AlirezaAsna/head-md-ai-families/images/final/IMG_3869.JPG

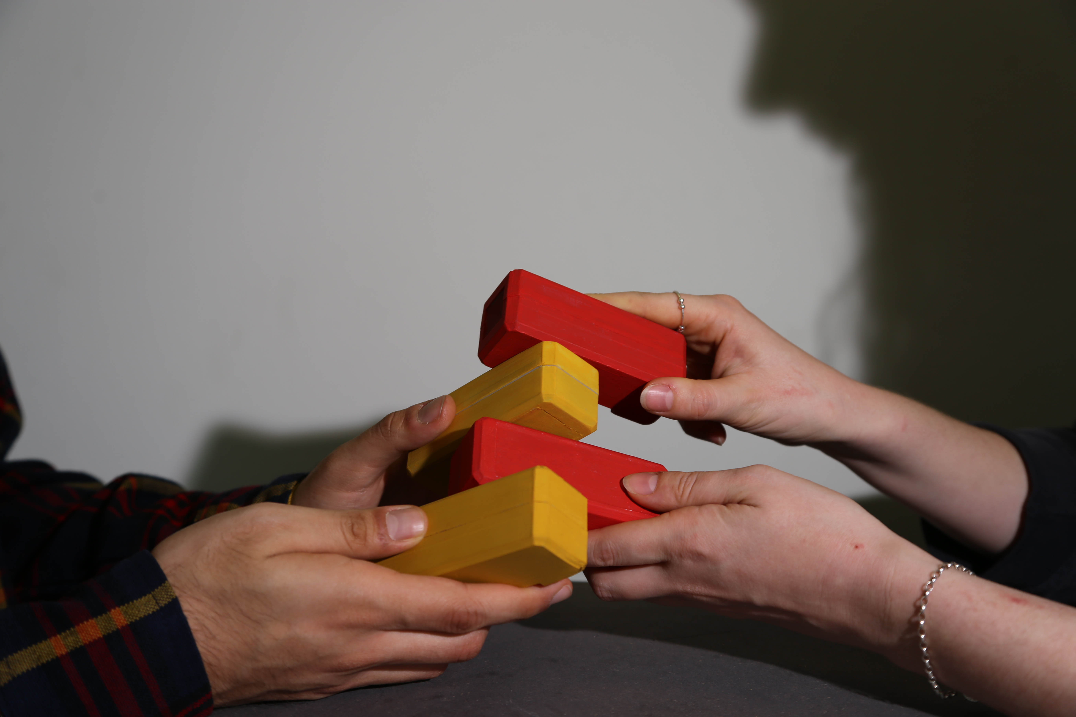
images/final/IMG_3869.JPG
