AlirezaAsna/head-md-ai-families/images/final/IMG_3872.JPG

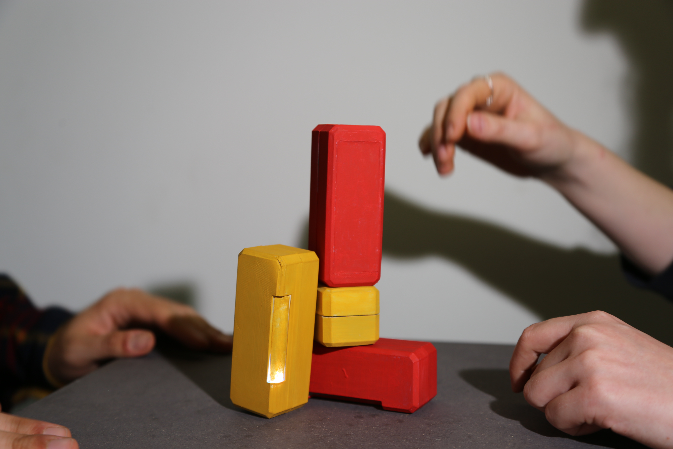
images/final/IMG_3872.JPG
