AlirezaAsna/head-md-ai-families/images/final/IMG_3876.JPG

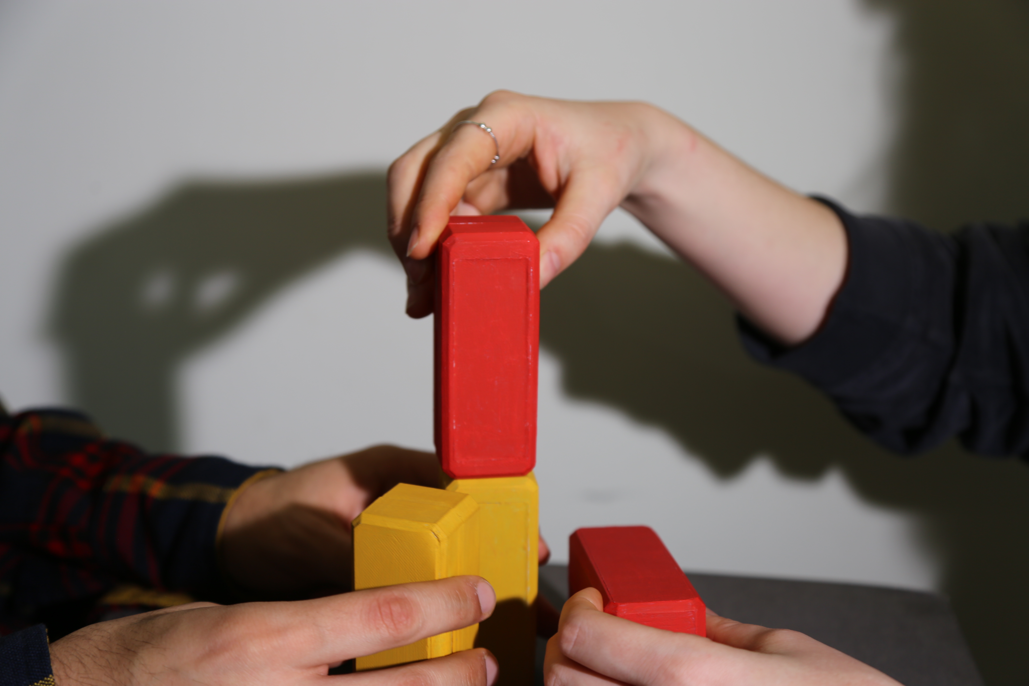
images/final/IMG_3876.JPG
