AlirezaAsna/head-md-ai-families/images/final/IMG_3880.JPG

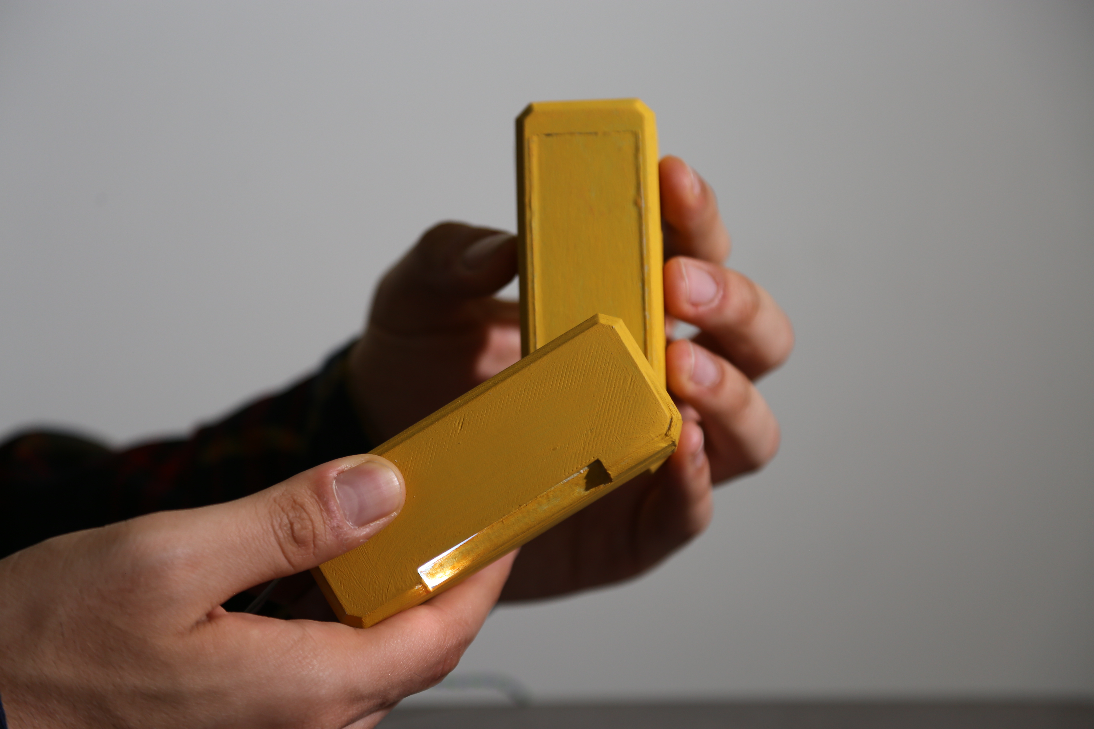
images/final/IMG_3880.JPG
