AlirezaAsna/head-md-ai-families/images/final/IMG_3882.JPG

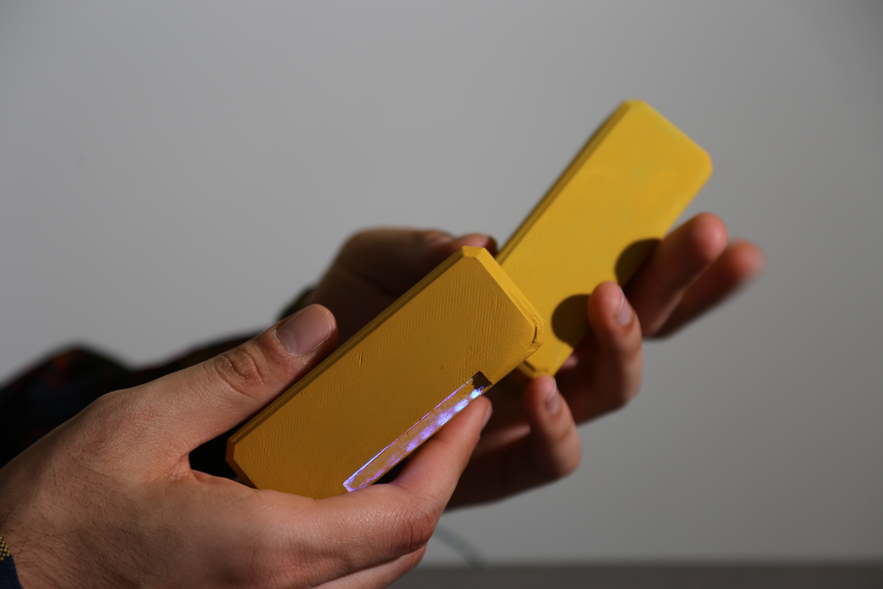
images/final/IMG_3882.JPG
