AlirezaAsna/head-md-ai-families/images/final/IMG_3889.JPG

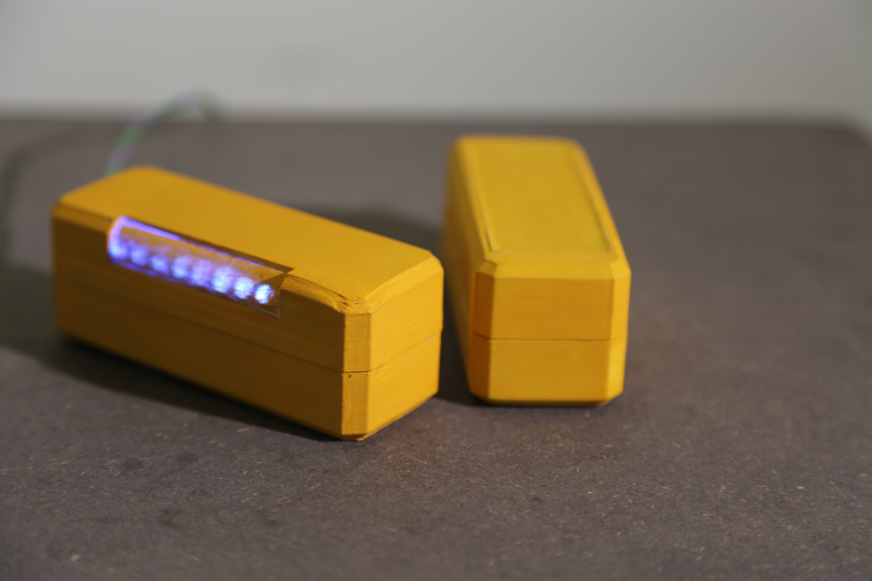
images/final/IMG_3889.JPG
