AlirezaAsna/head-md-ai-families/images/final/IMG_3912.JPG

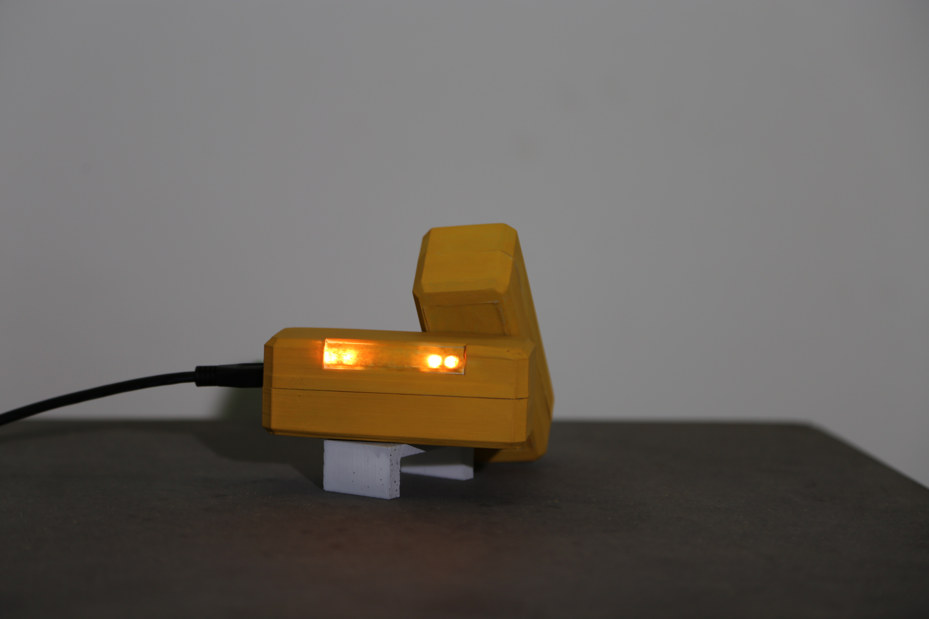
images/final/IMG_3912.JPG
