AlirezaAsna/head-md-ai-families/images/ideation/IMG_3755.JPG

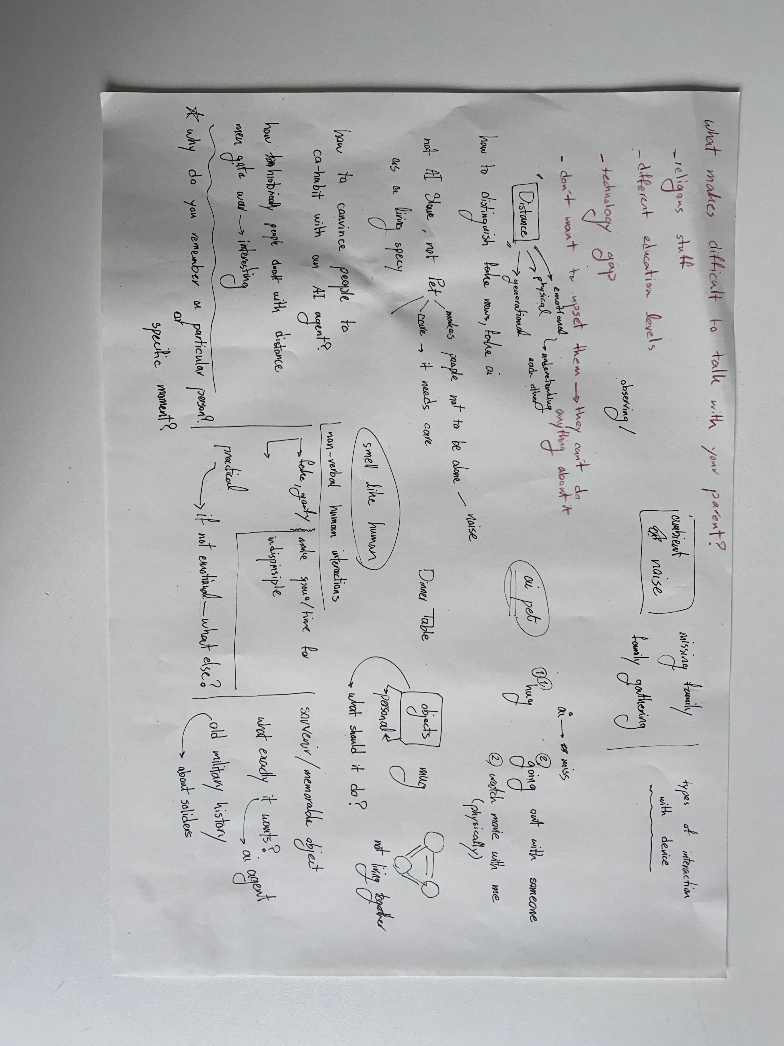
images/ideation/IMG_3755.JPG
