AlirezaAsna/head-md-ai-families/images/ideation/IMG_3756.JPG

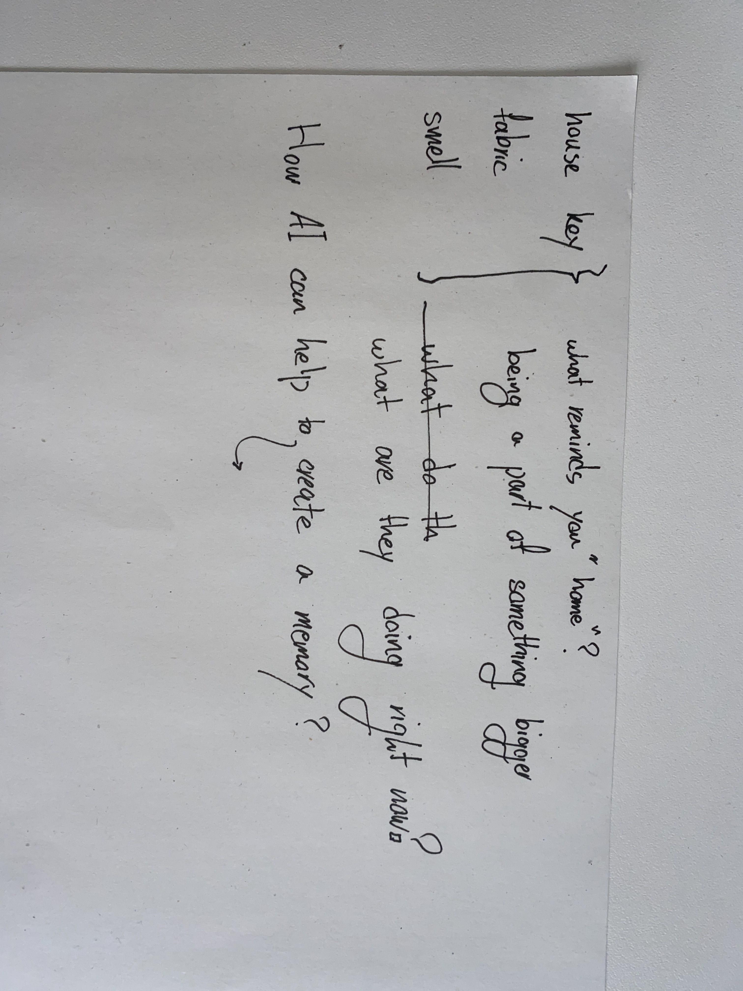
images/ideation/IMG_3756.JPG
