AlirezaAsna/head-md-ai-families/images/ideation/IMG_3757.JPG

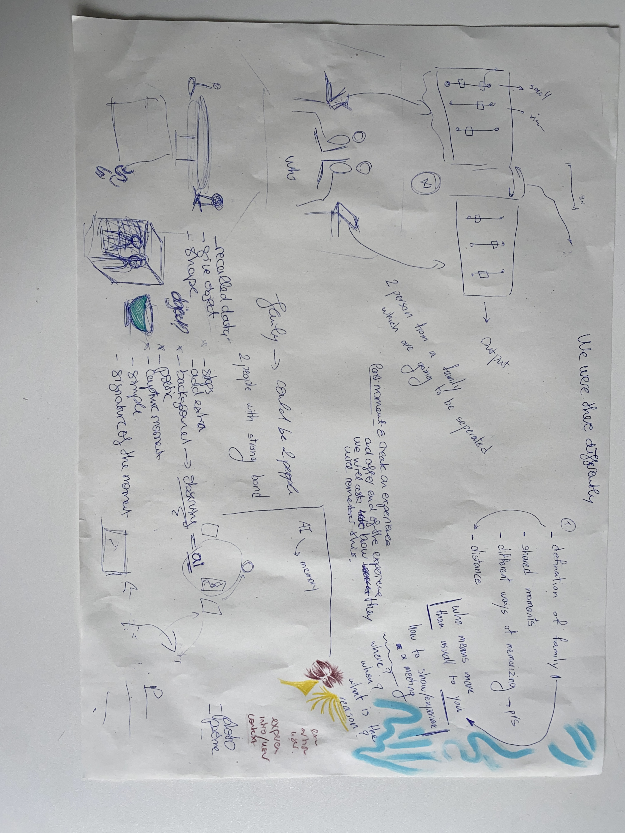
images/ideation/IMG_3757.JPG
