AlirezaAsna/head-md-ai-families/images/ideation/IMG_3758.JPG

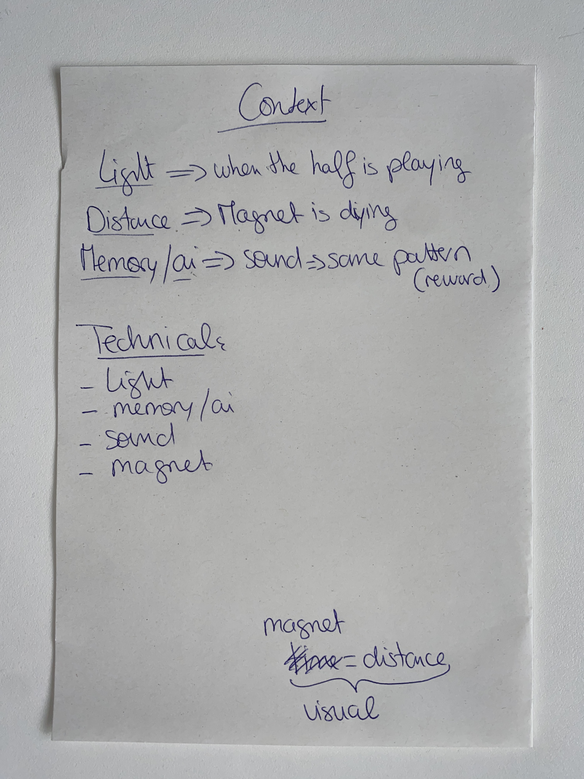
images/ideation/IMG_3758.JPG
