AlirezaAsna/head-md-ai-families/images/ideation/IMG_3759.JPG

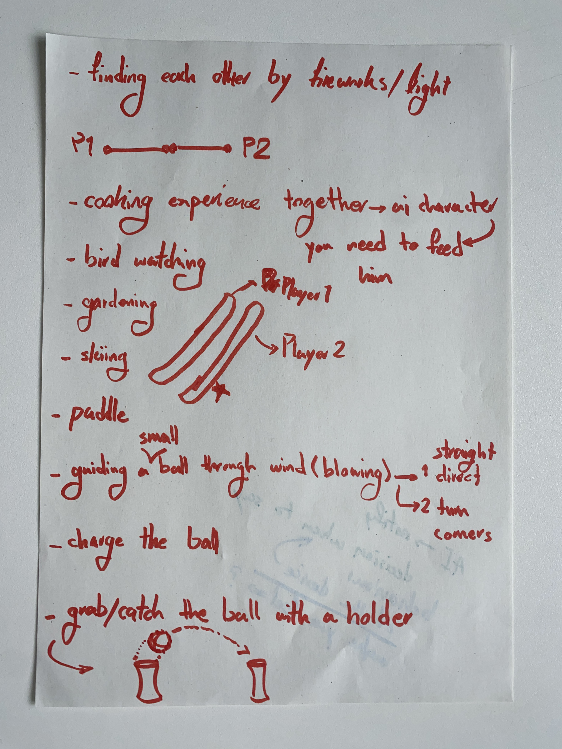
images/ideation/IMG_3759.JPG
