AlirezaAsna/head-md-ai-families/images/ideation/IMG_3760.JPG

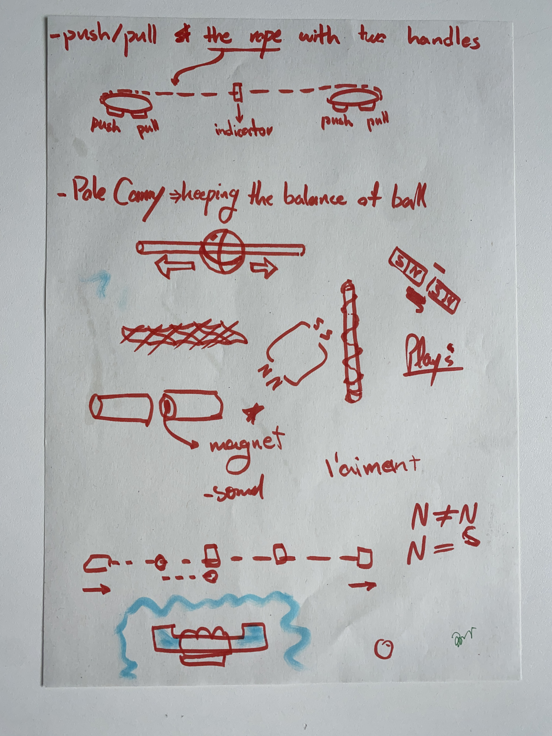
images/ideation/IMG_3760.JPG
