AlirezaAsna/head-md-ai-families/images/ideation/IMG_3761.JPG

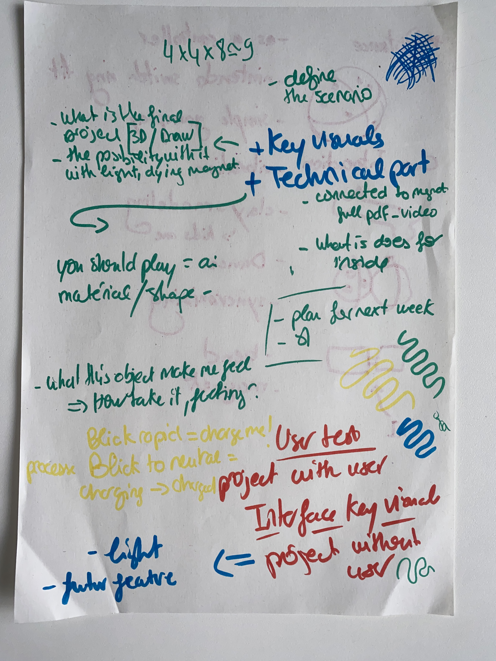
images/ideation/IMG_3761.JPG
