AlirezaAsna/head-md-ai-families/images/ideation/IMG_3762.JPG

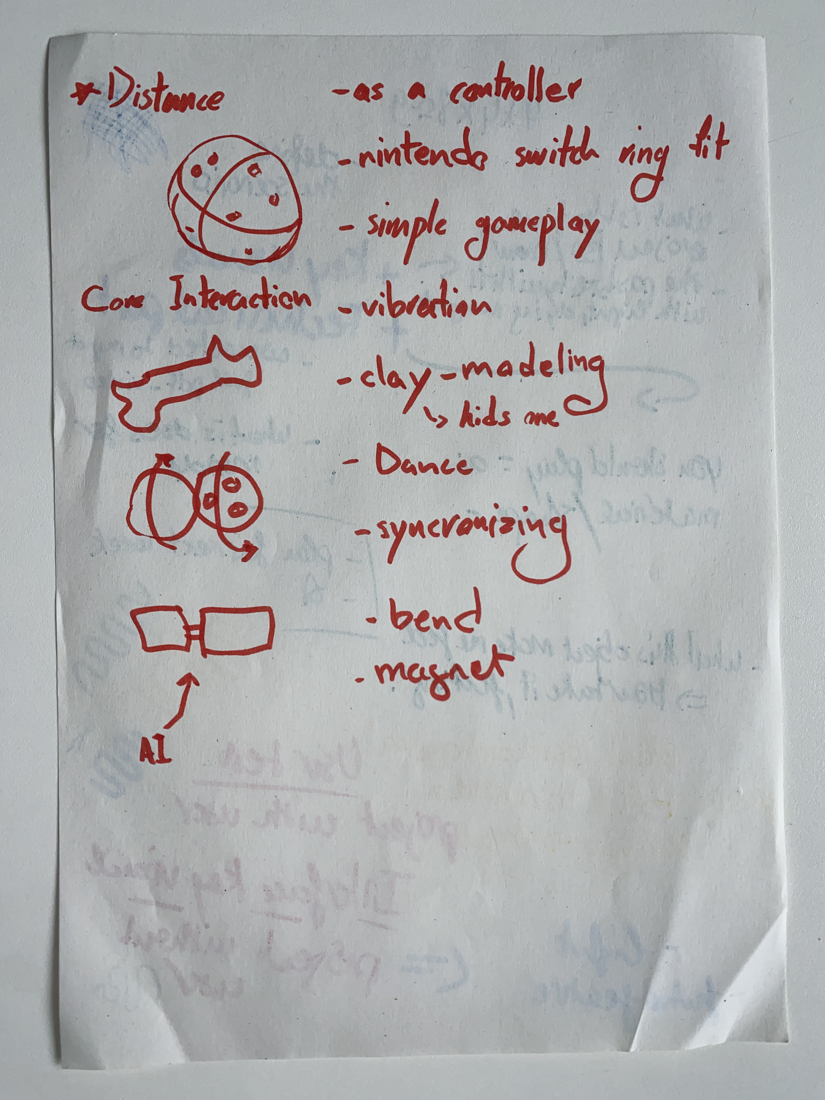
images/ideation/IMG_3762.JPG
