AlirezaAsna/head-md-ai-families/images/ideation/IMG_3763.JPG

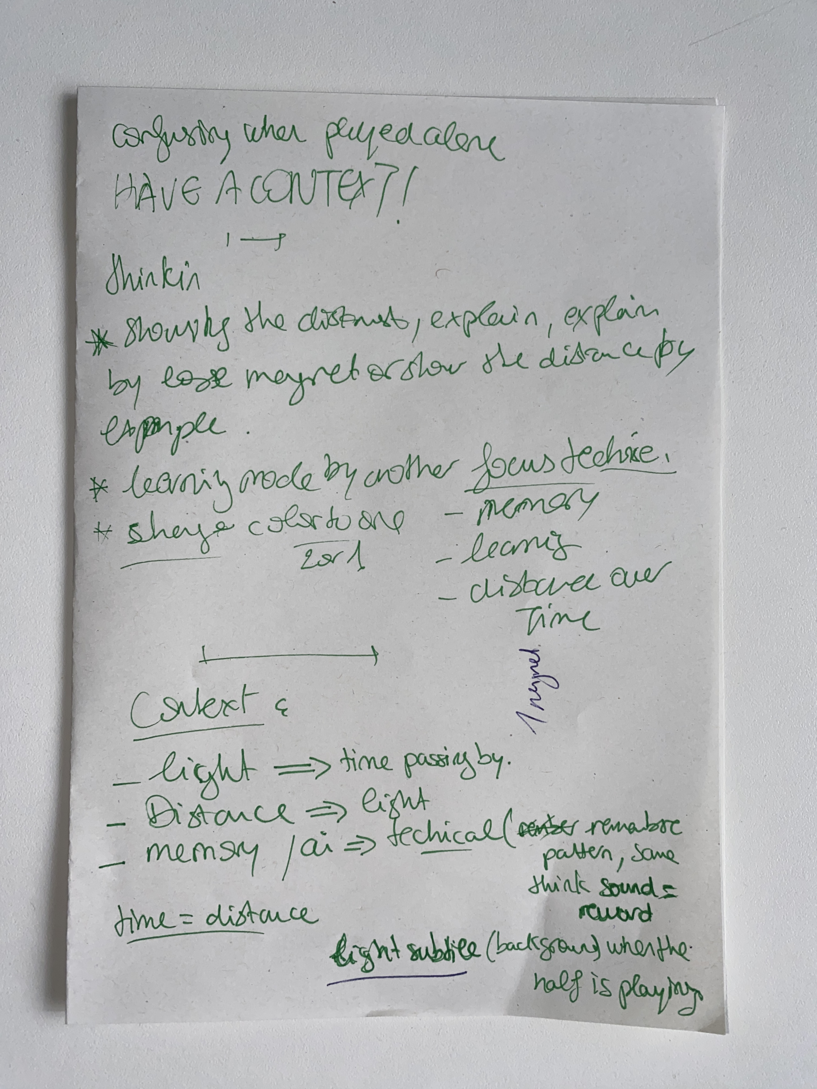
images/ideation/IMG_3763.JPG
