AlirezaAsna/head-md-ai-families/images/ideation/IMG_3764.JPG

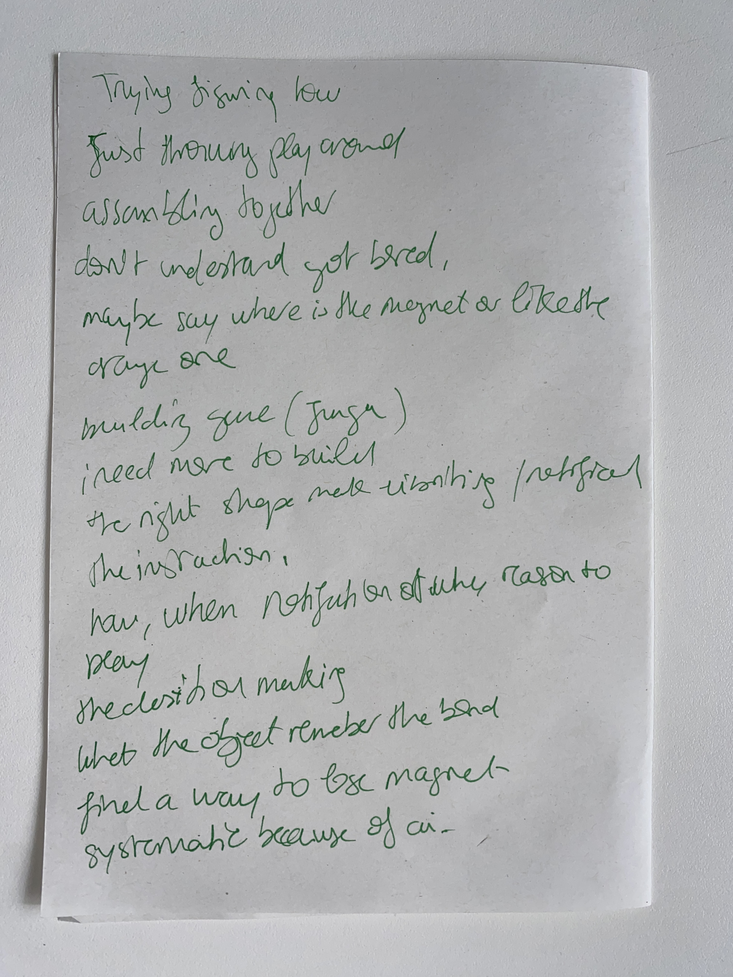
images/ideation/IMG_3764.JPG
