AlirezaAsna/head-md-ai-families/images/ideation/IMG_3765.JPG

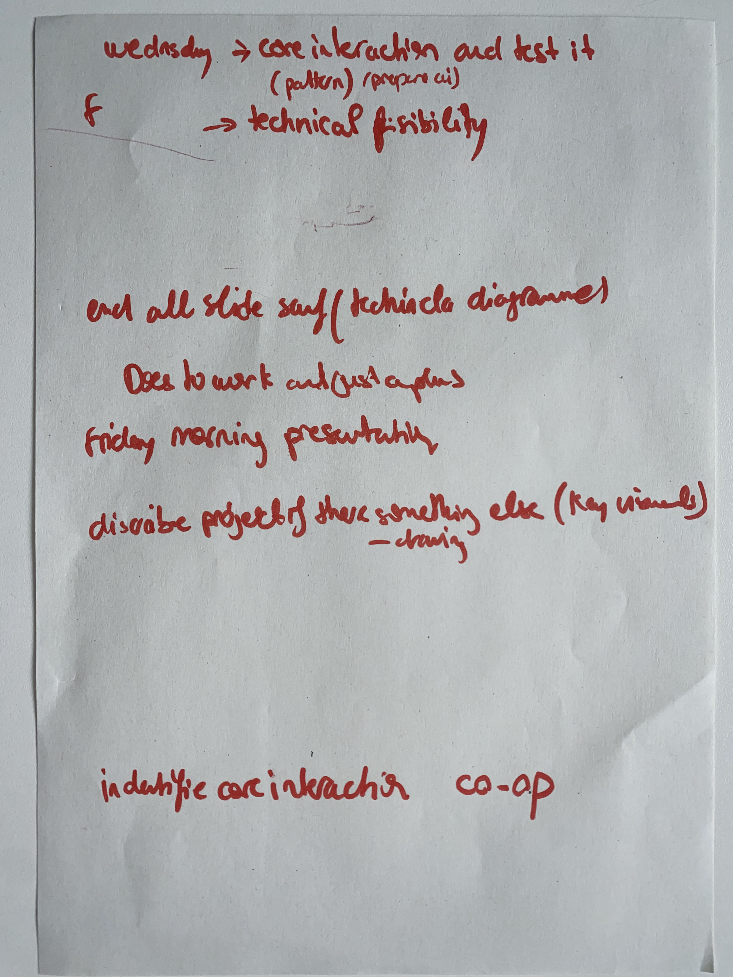
images/ideation/IMG_3765.JPG
