AlirezaAsna/head-md-ai-families/images/ideation/IMG_3766.JPG

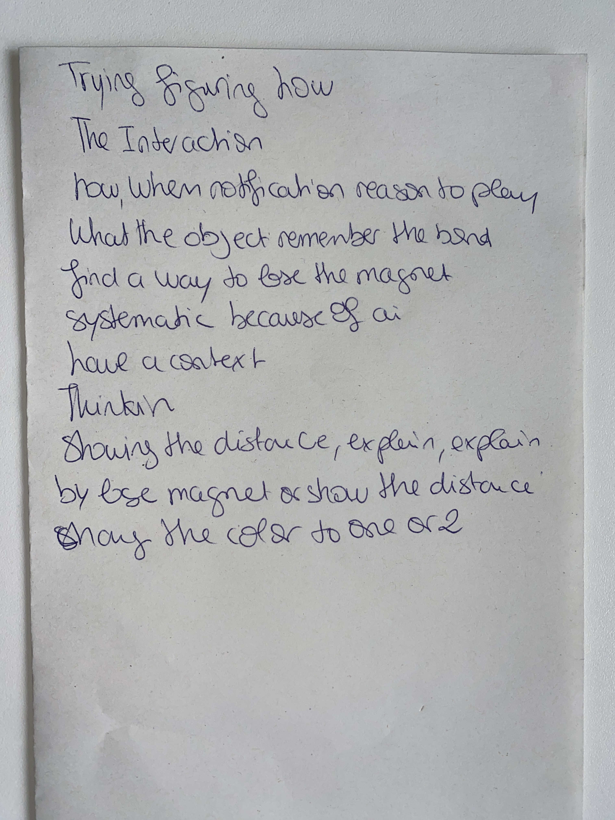
images/ideation/IMG_3766.JPG
