AlirezaAsna/head-md-ai-families/images/ideation/IMG_3767.JPG

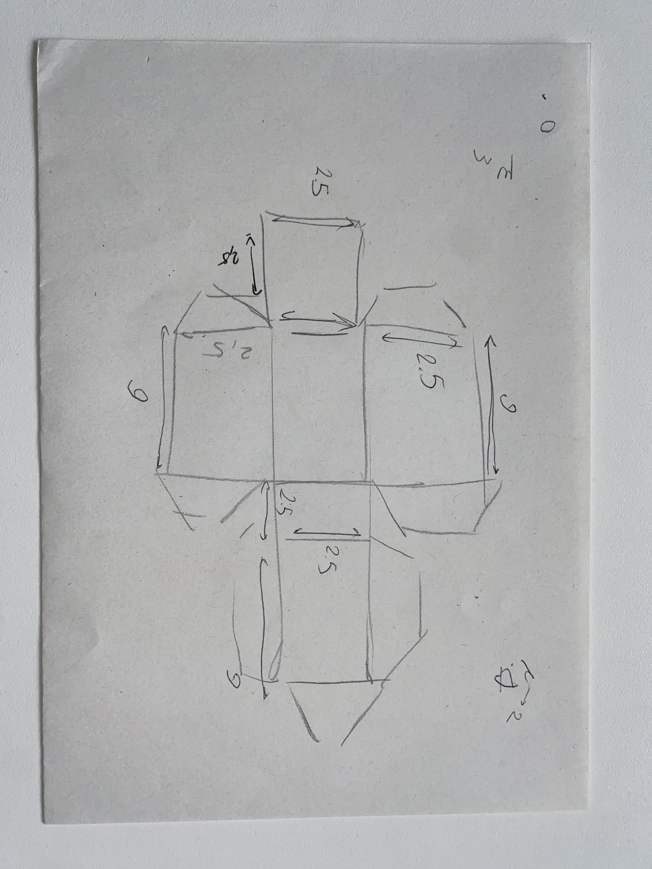
images/ideation/IMG_3767.JPG
