AlirezaAsna/head-md-ai-families/images/ideation/IMG_3768.JPG

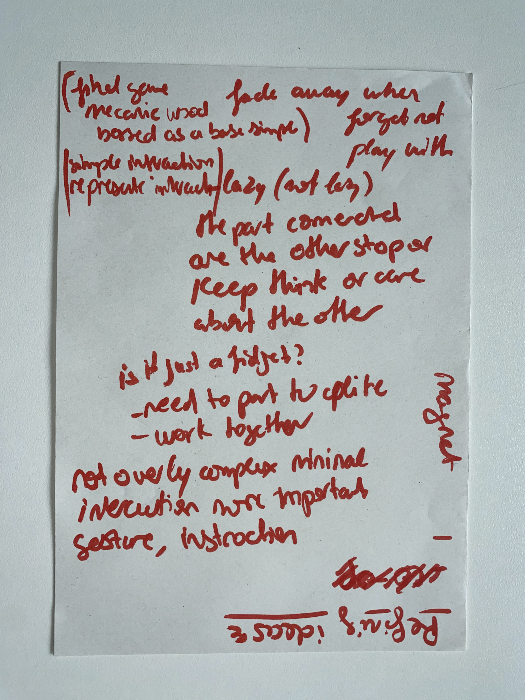
images/ideation/IMG_3768.JPG
