AlirezaAsna/head-md-ai-families/images/ideation/IMG_3770.JPG

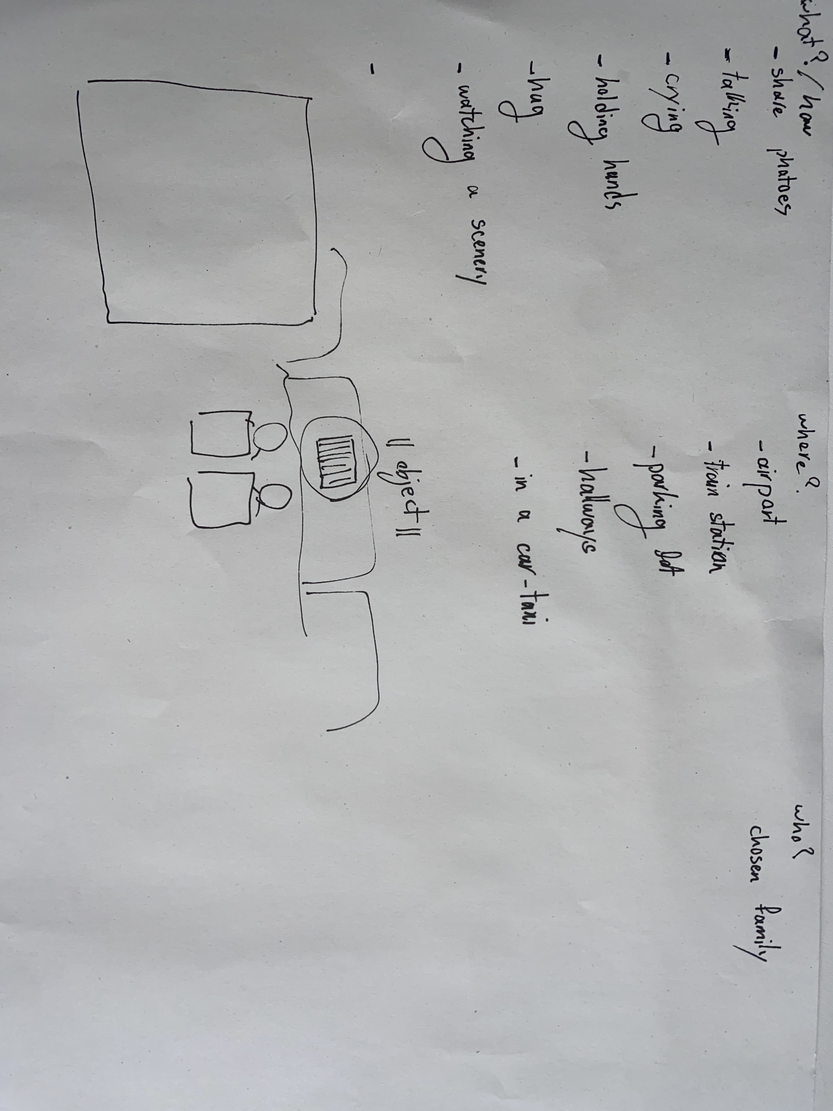
images/ideation/IMG_3770.JPG
