AlirezaAsna/head-md-ai-families/images/ideation/IMG_3771.JPG

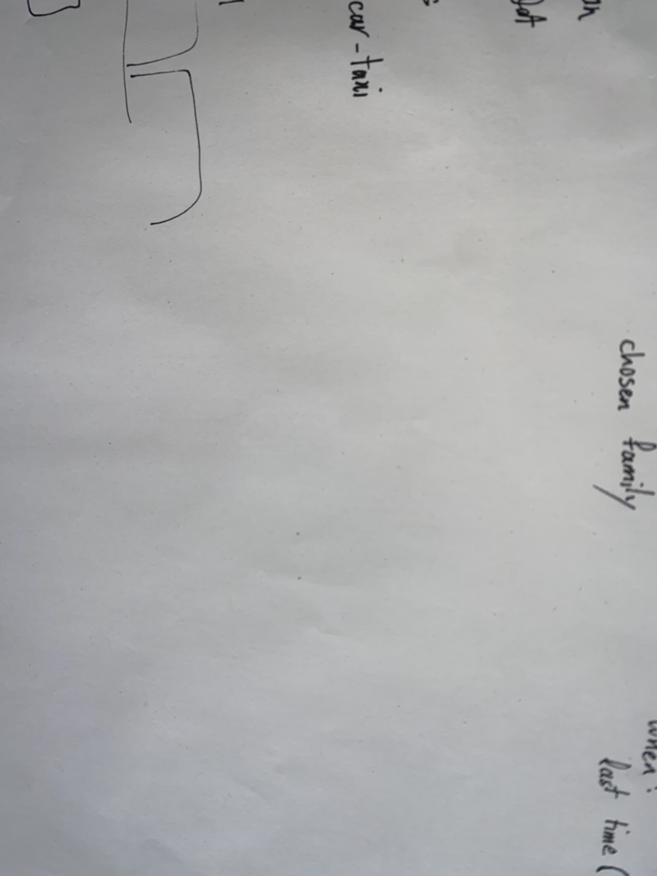
images/ideation/IMG_3771.JPG
