AlirezaAsna/head-md-ai-families/images/ideation/IMG_3772.JPG

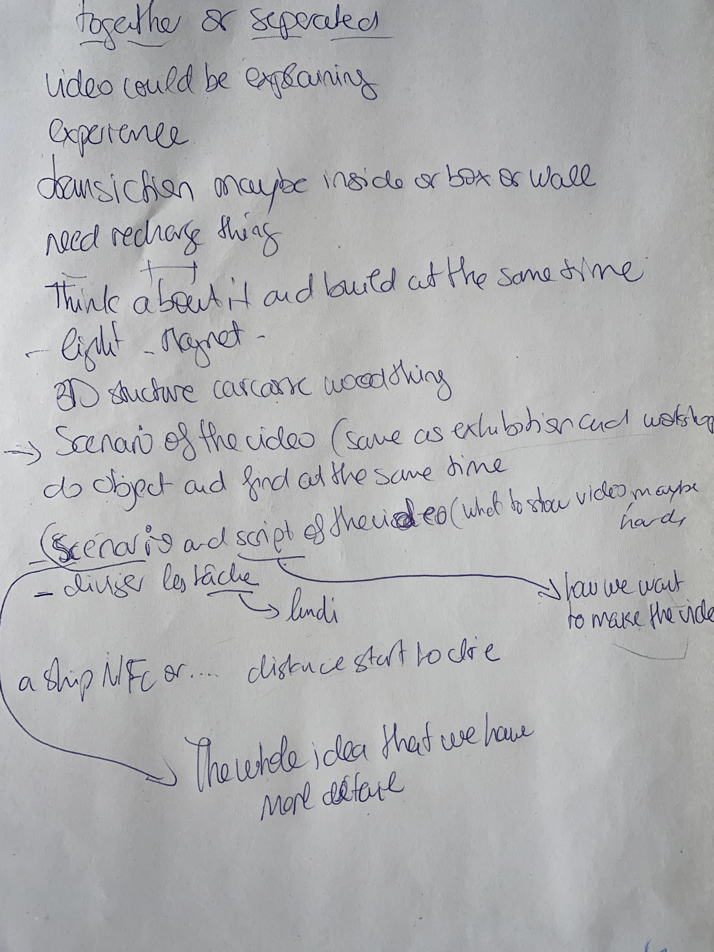
images/ideation/IMG_3772.JPG
