AlirezaAsna/head-md-ai-families/images/ideation/IMG_3773.JPG

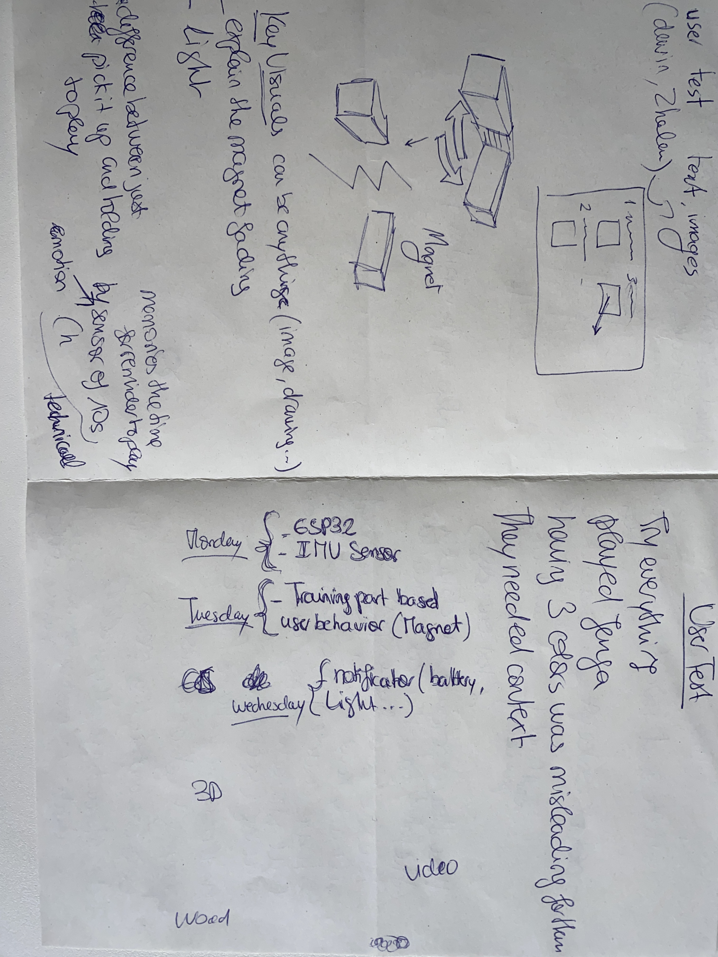
images/ideation/IMG_3773.JPG
