AlirezaAsna/head-md-ai-families/images/ideation/IMG_3774.JPG

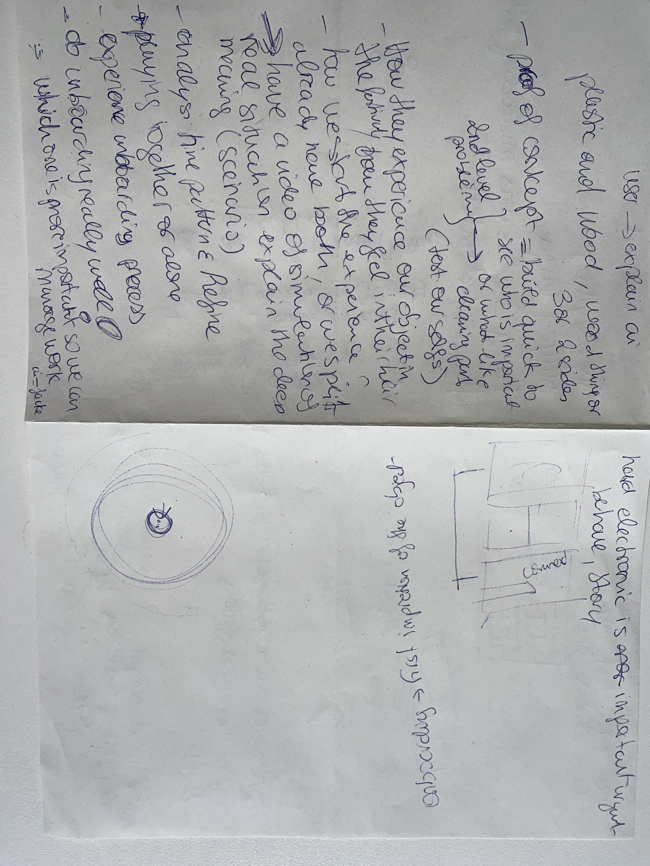
images/ideation/IMG_3774.JPG
