AlirezaAsna/head-md-ai-families/images/ideation/photo_2026-03-13_14-27-43.jpg

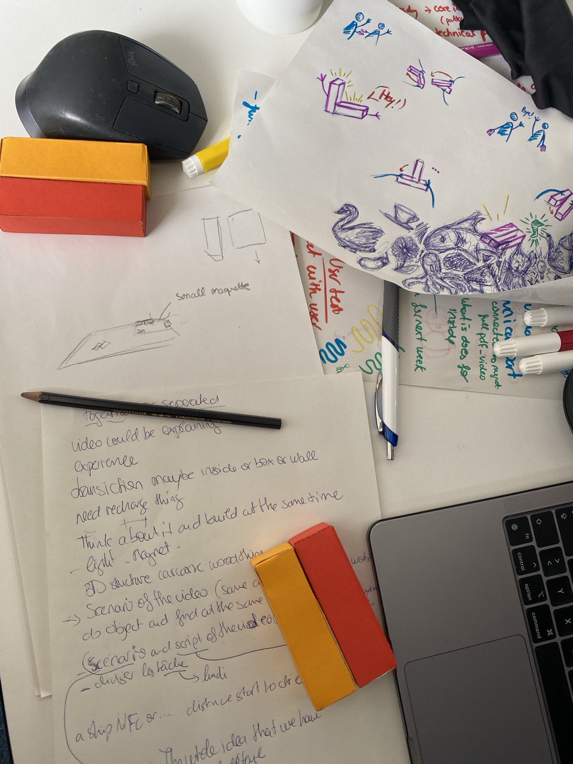
images/ideation/photo_2026-03-13_14-27-43.jpg
