AlirezaAsna/head-md-ai-families/images/process/IMG_3687.JPG

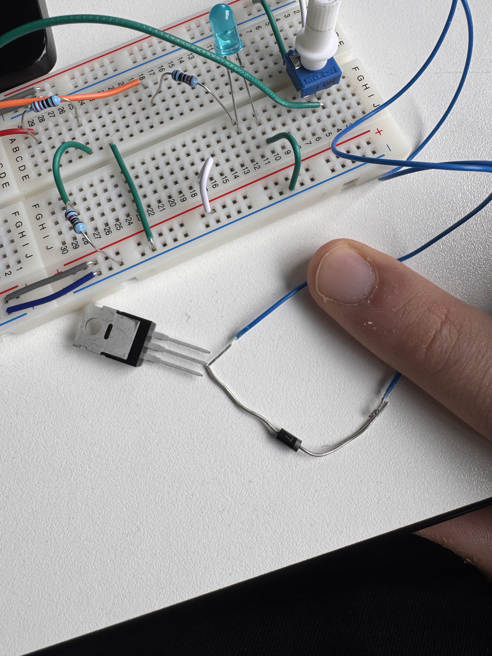
images/process/IMG_3687.JPG
