AlirezaAsna/head-md-ai-families/images/process/IMG_3693.JPG

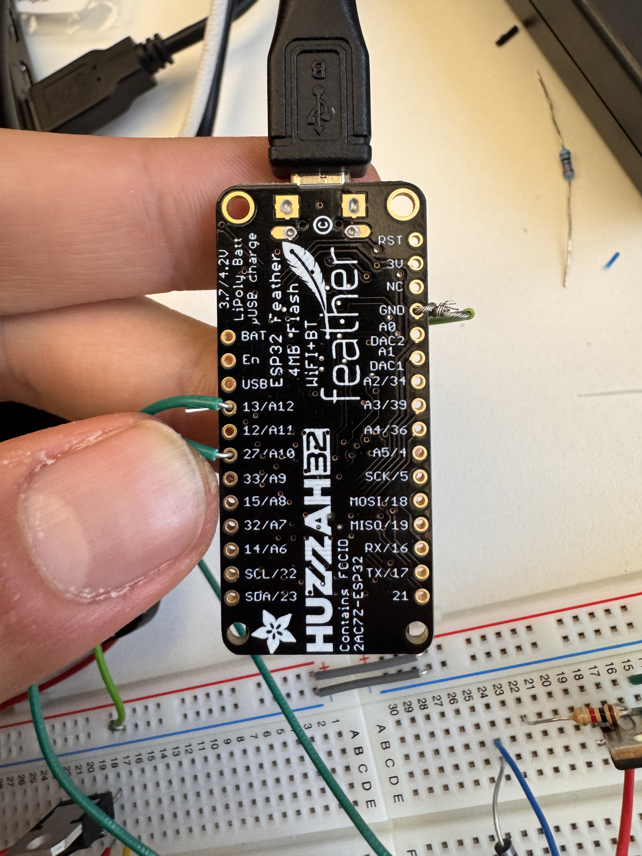
images/process/IMG_3693.JPG
