AlirezaAsna/head-md-ai-families/images/process/IMG_3699.JPG

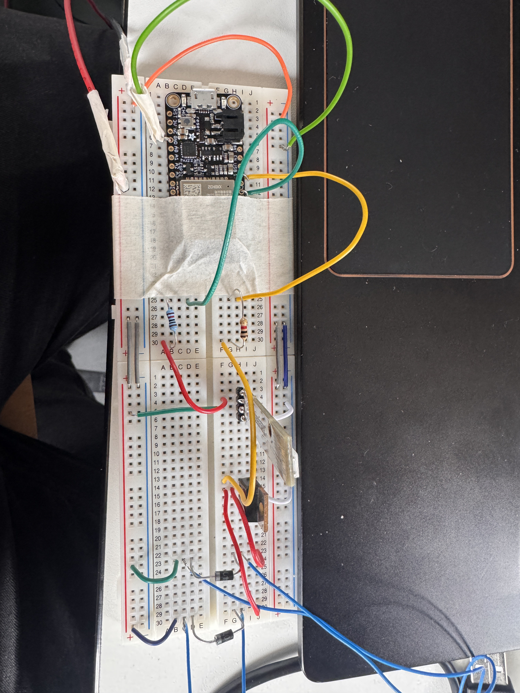
images/process/IMG_3699.JPG
