AlirezaAsna/head-md-ai-families/images/process/IMG_3701.JPEG

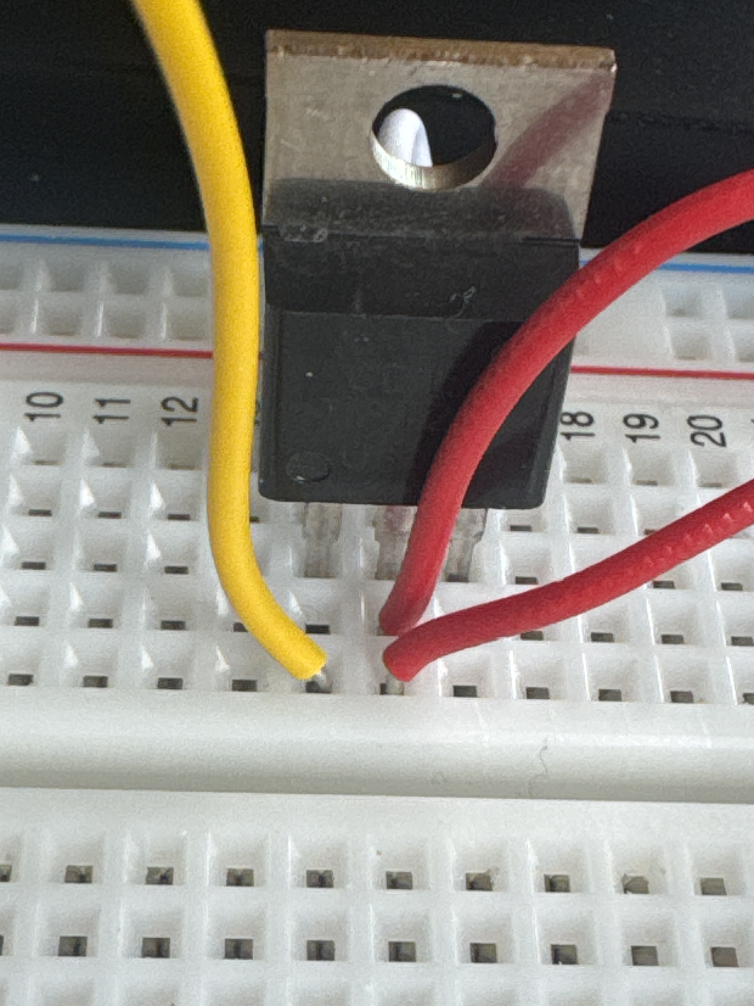
images/process/IMG_3701.JPEG
