AlirezaAsna/head-md-ai-families/images/process/IMG_3702.JPG

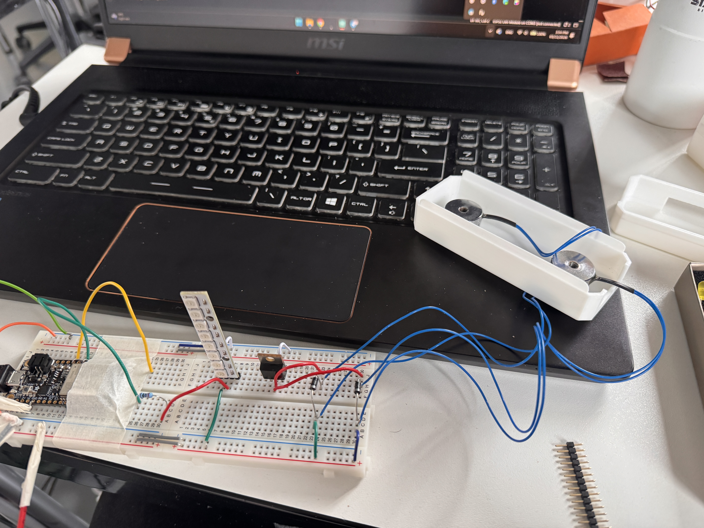
images/process/IMG_3702.JPG
