AlirezaAsna/head-md-ai-families/images/process/IMG_3703.JPG

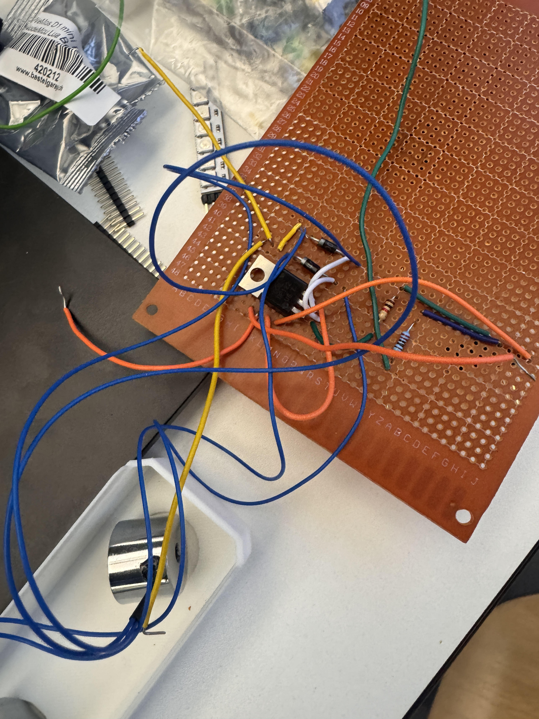
images/process/IMG_3703.JPG
