AlirezaAsna/head-md-ai-families/images/process/IMG_3715.JPG

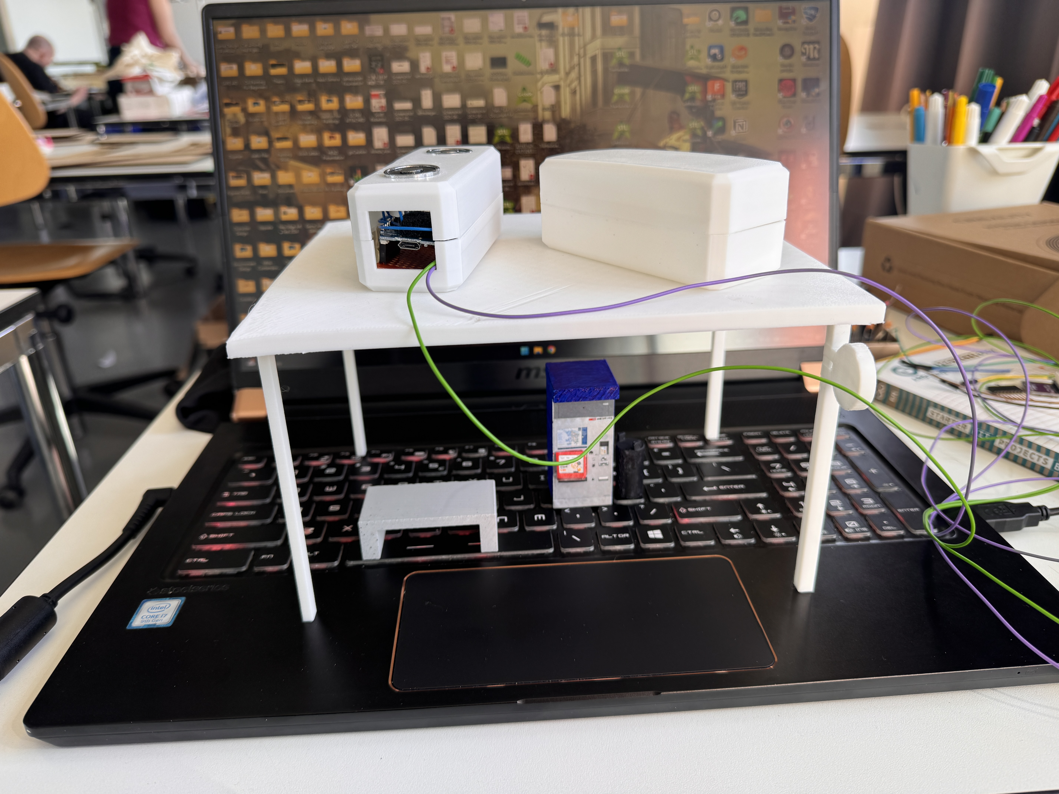
images/process/IMG_3715.JPG
