AlirezaAsna/head-md-ai-families/images/process/IMG_3724.JPG

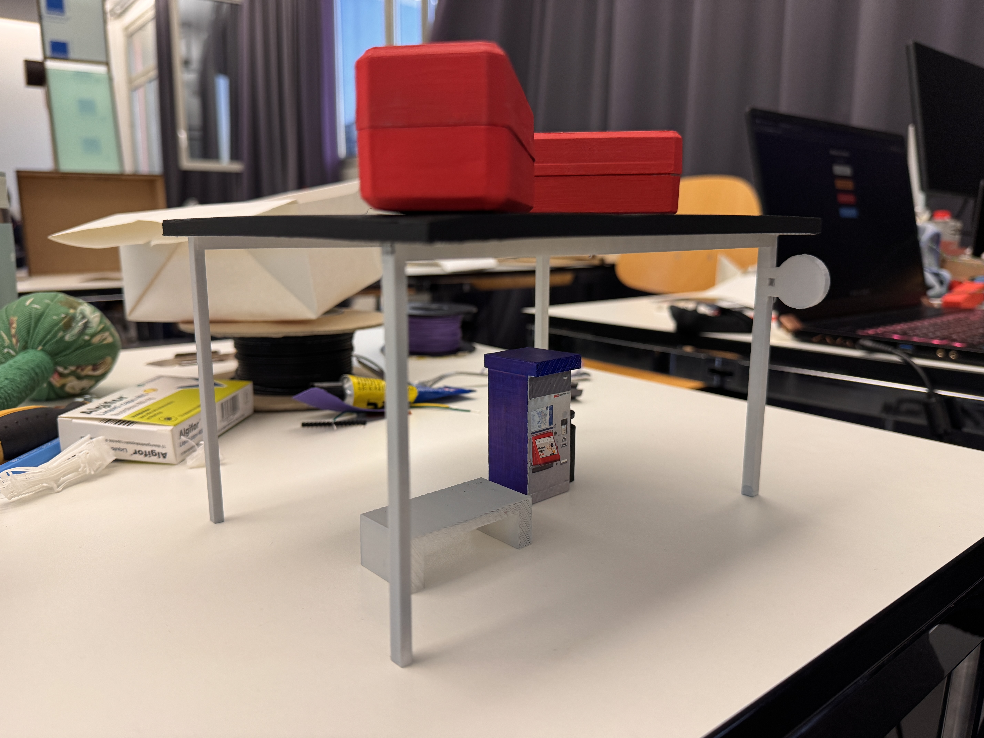
images/process/IMG_3724.JPG
