AlirezaAsna/head-md-ai-families/images/process/IMG_3725.JPG

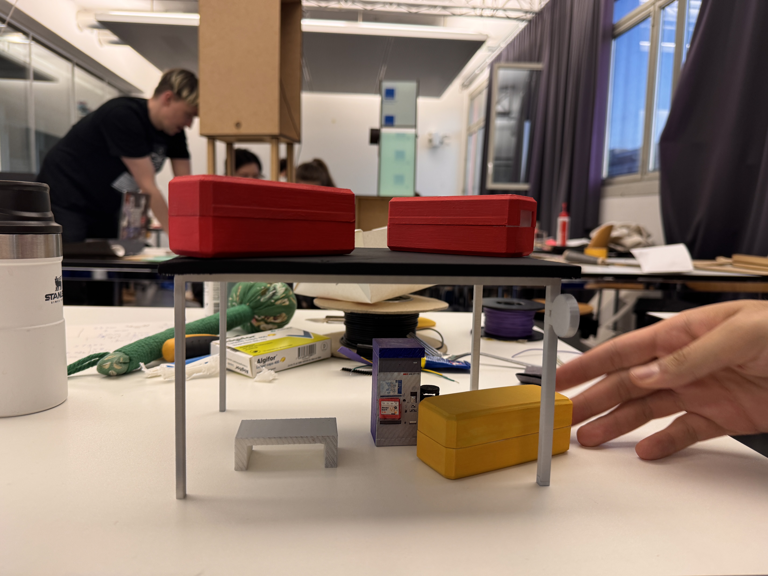
images/process/IMG_3725.JPG
