AlirezaAsna/head-md-ai-families/images/process/IMG_3727.JPG

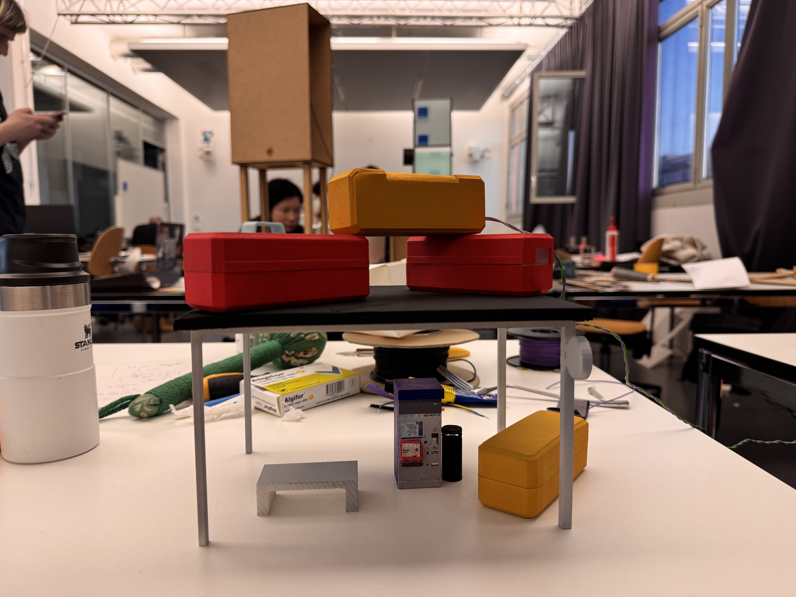
images/process/IMG_3727.JPG
