AlirezaAsna/head-md-ai-families/images/process/IMG_3728.JPG

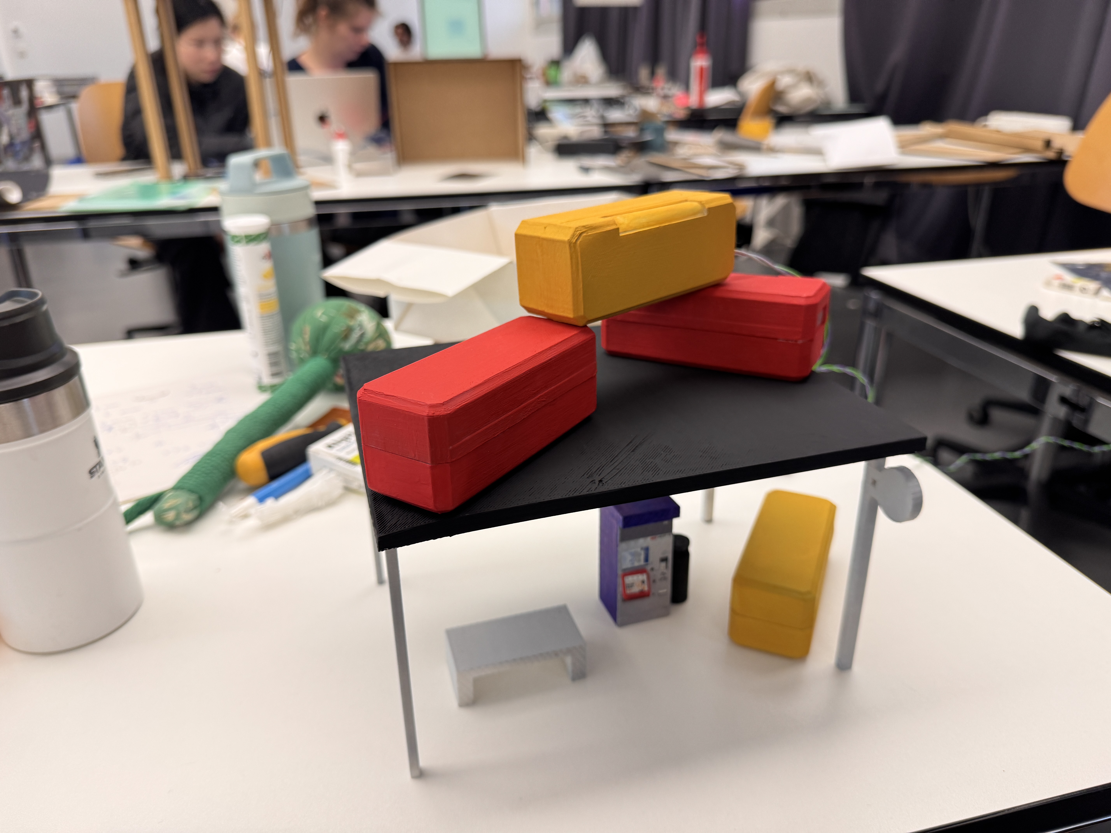
images/process/IMG_3728.JPG
