AlirezaAsna/head-md-ai-families/images/process/photo_2026-03-13_14-27-32.jpg

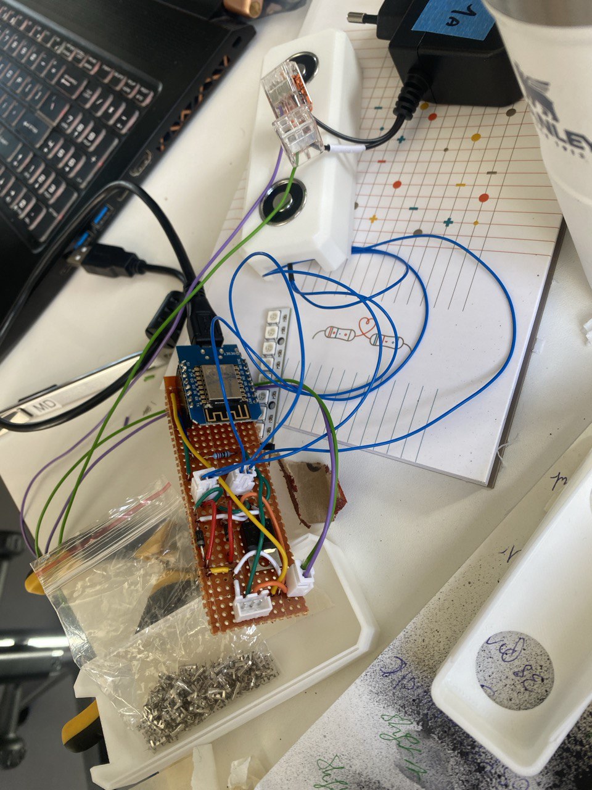
images/process/photo_2026-03-13_14-27-32.jpg
