AlirezaAsna/head-md-ai-families/images/renders/lightsOff.png

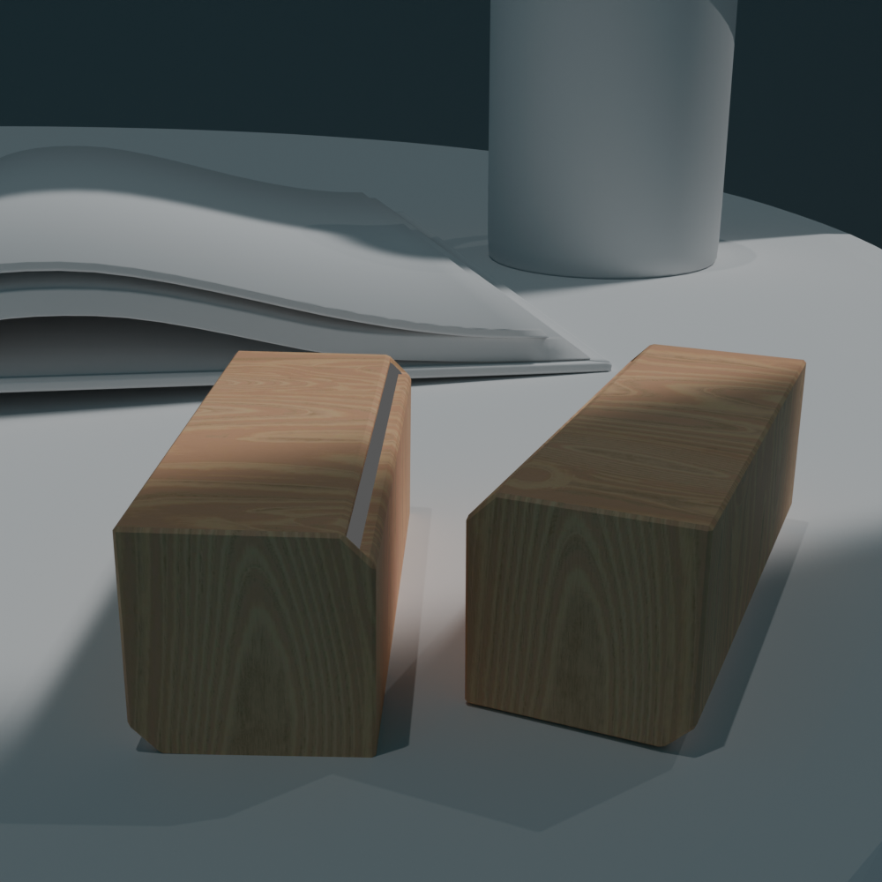
images/renders/lightsOff.png
