AlirezaAsna/head-md-ai-families/images/technical-diagram/technical diagram.png

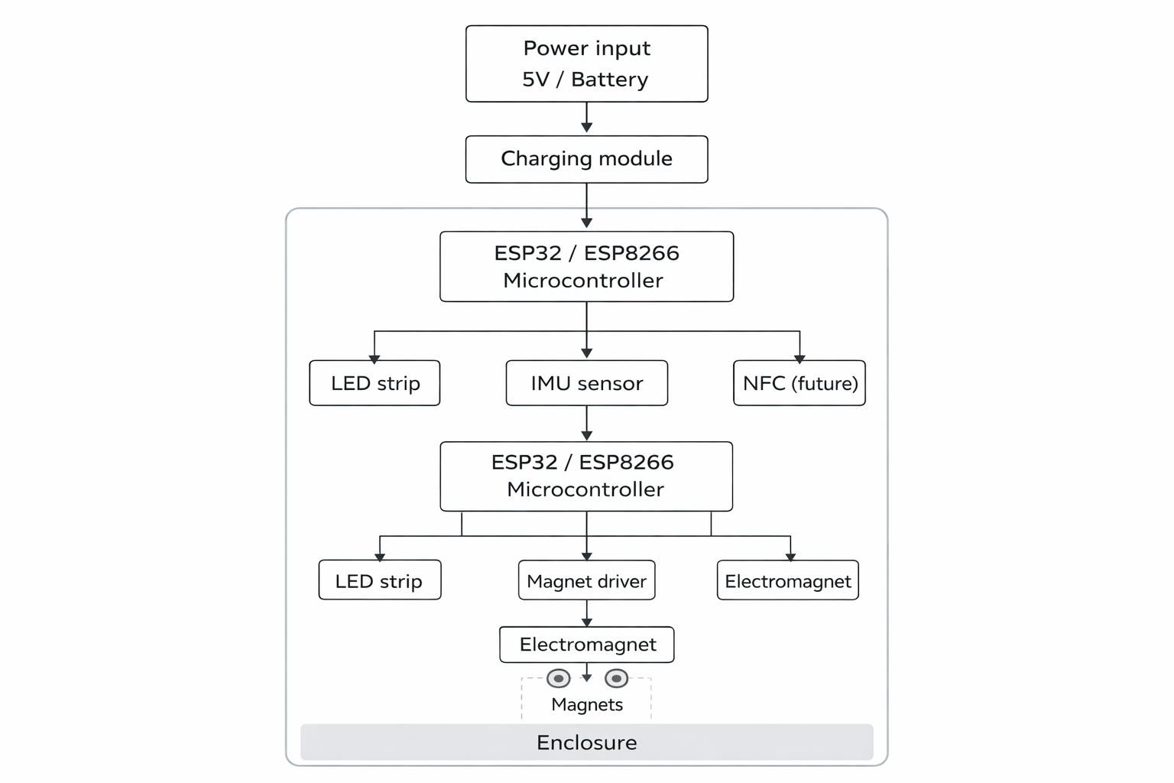
images/technical-diagram/technical diagram.png
