AlirezaAsna/head-md-ai-families/images/ideation/IMG_3754.JPG

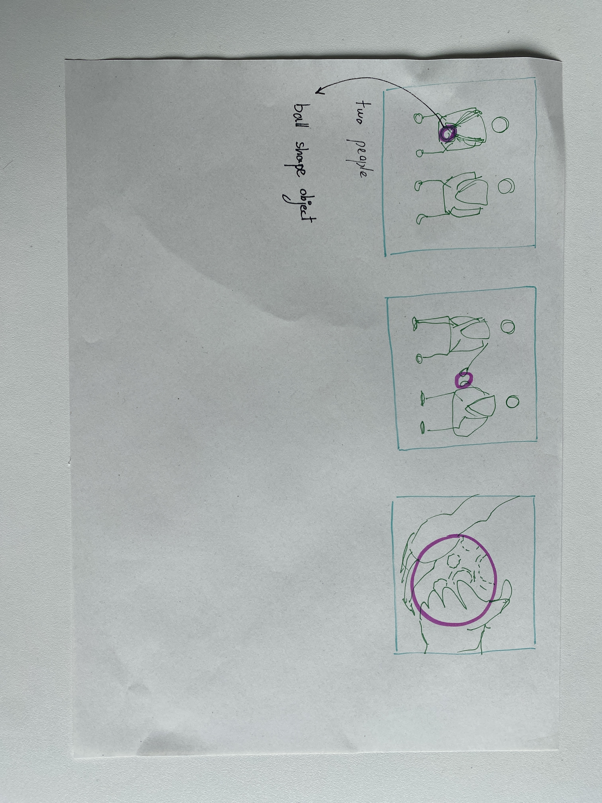
images/ideation/IMG_3754.JPG
