AlirezaAsna/head-md-ai-families/images/ideation/IMG_3769.JPG

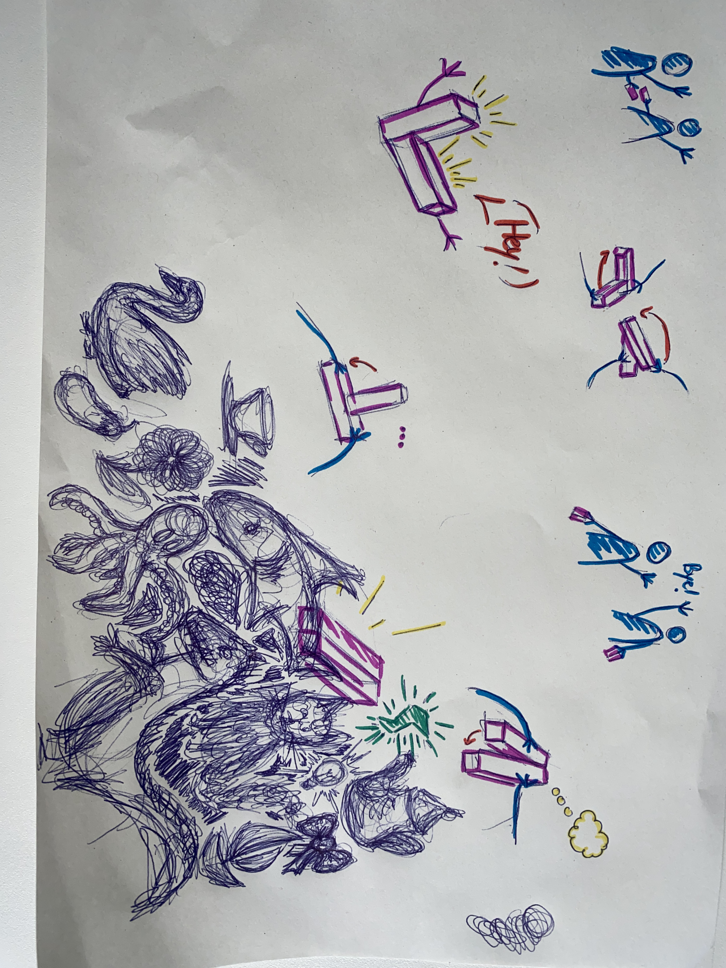
images/ideation/IMG_3769.JPG
