AlirezaAsna/head-md-ai-families/images/process/IMG_3681.JPG

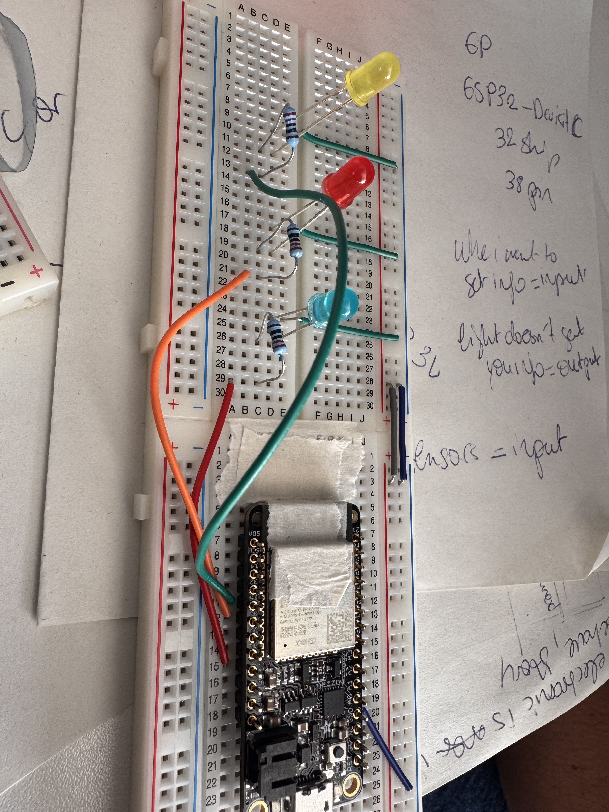
images/process/IMG_3681.JPG
