AlirezaAsna/head-md-ai-families/images/process/IMG_3685.JPG

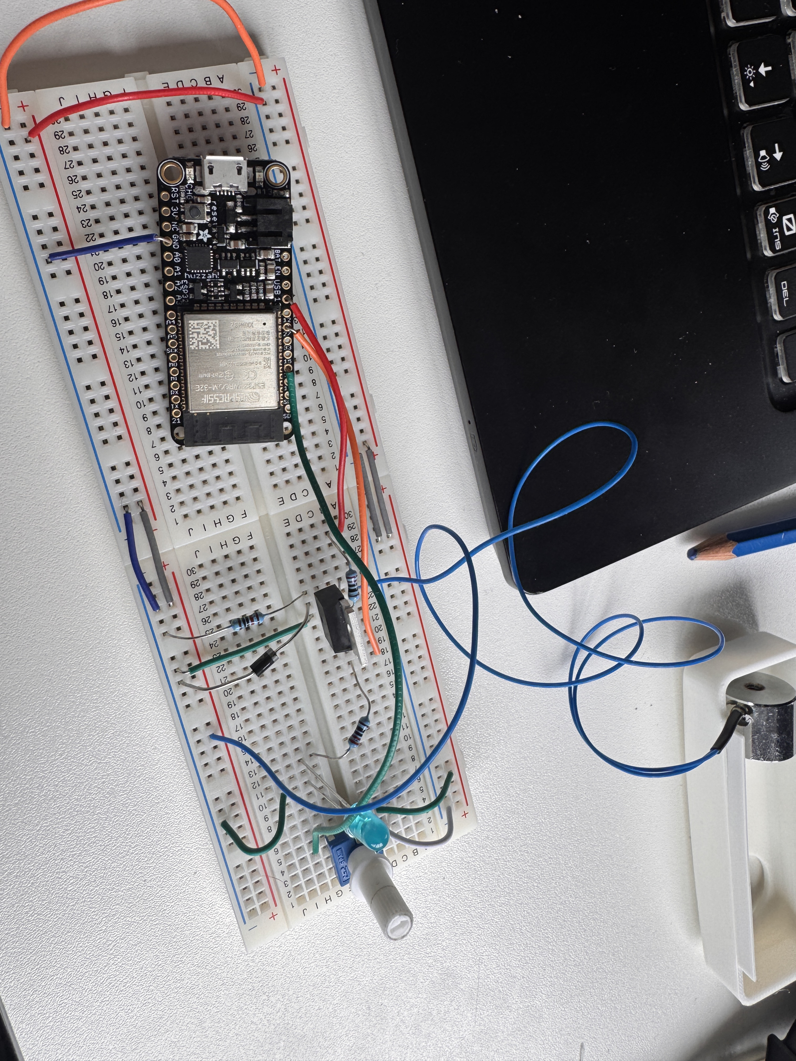
images/process/IMG_3685.JPG
