AlirezaAsna/head-md-ai-families/images/process/IMG_3688.JPG

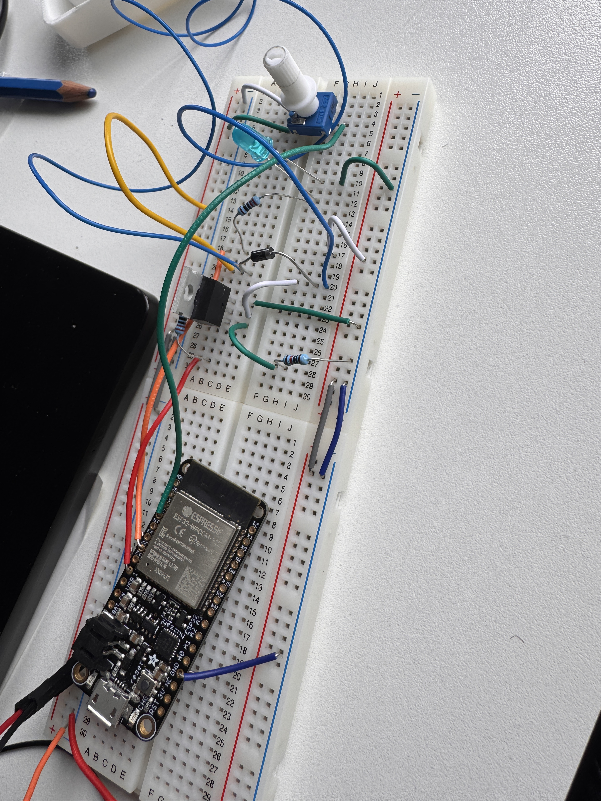
images/process/IMG_3688.JPG
