AlirezaAsna/head-md-ai-families/images/process/IMG_3689.JPG

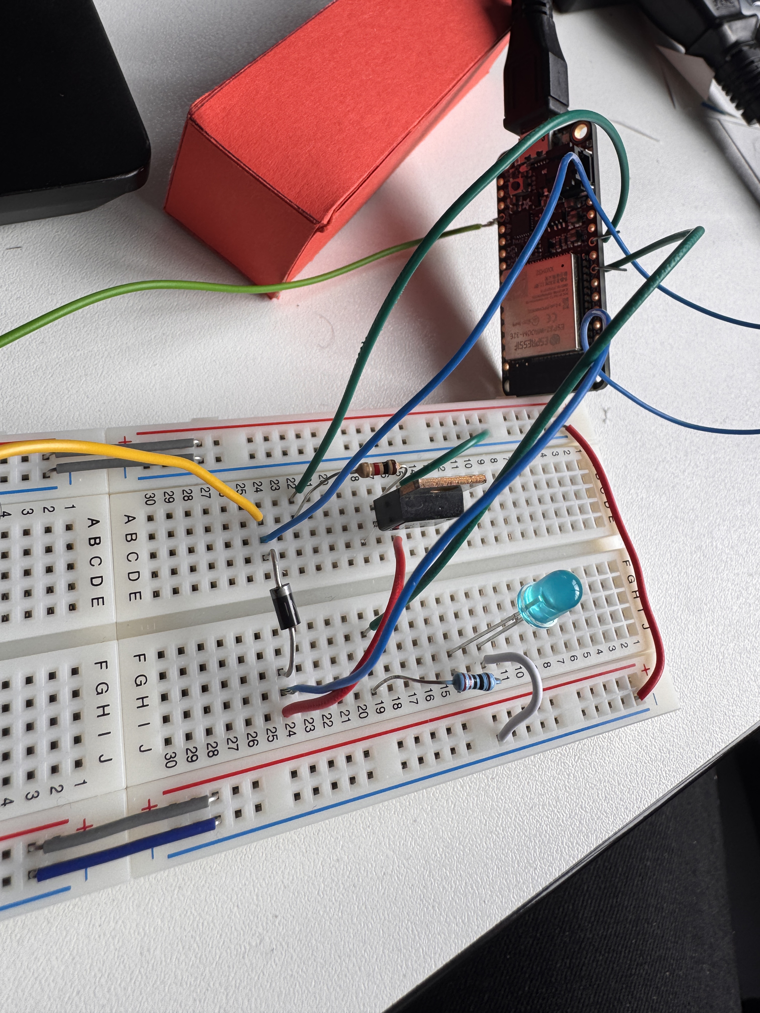
images/process/IMG_3689.JPG
