AlirezaAsna/head-md-ai-families/images/process/IMG_3690.JPG

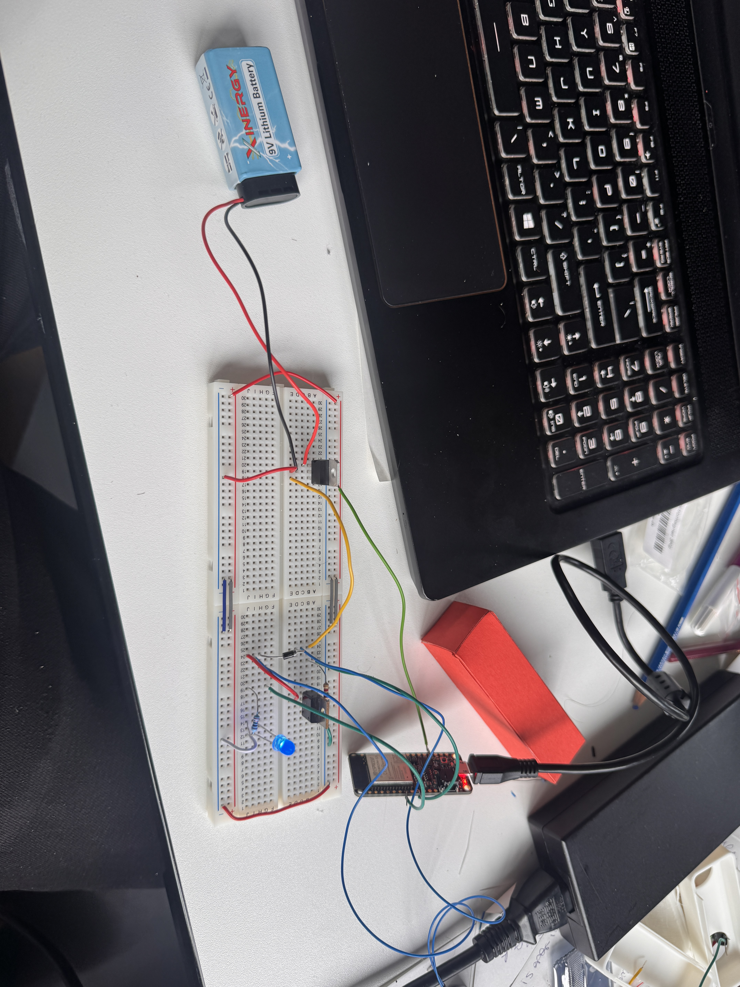
images/process/IMG_3690.JPG
