AlirezaAsna/head-md-ai-families/images/process/IMG_3716.JPG

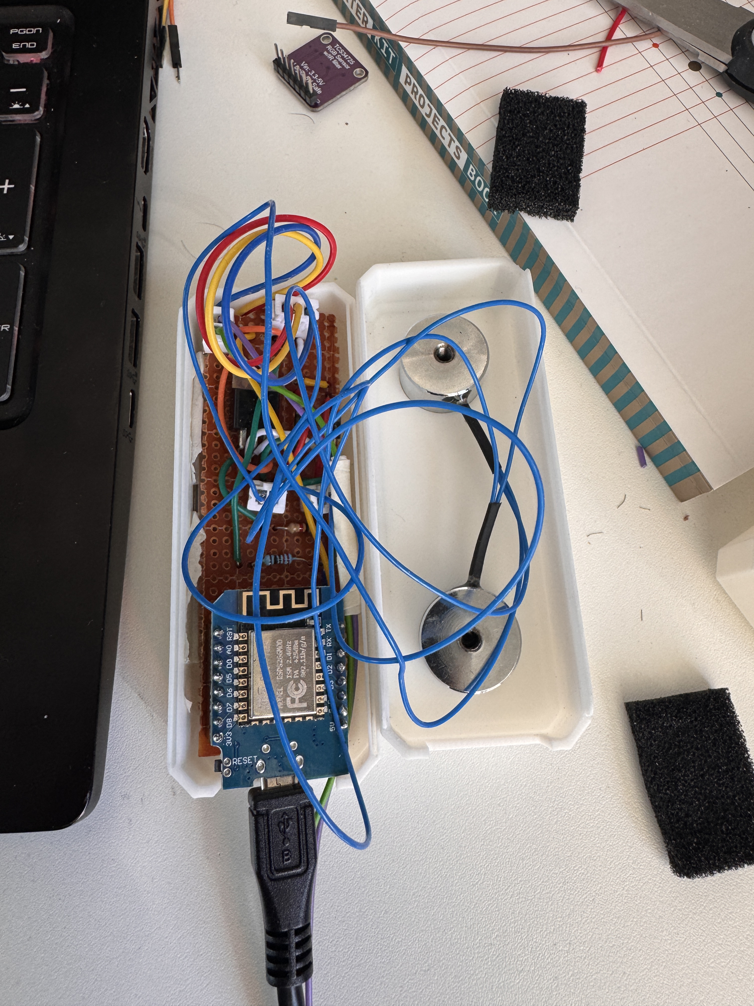
images/process/IMG_3716.JPG
